nickehallgren/halpis-intcm/hw/bp/images/2024_7_battery_connector_v1_1_3d.png

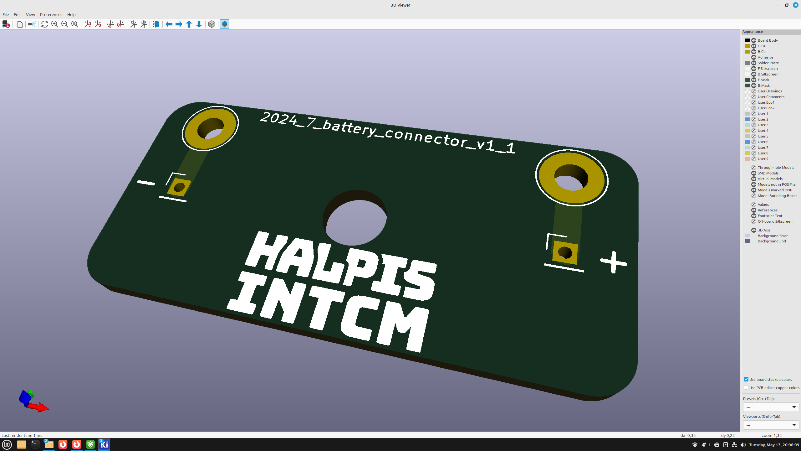
hw/bp/images/2024_7_battery_connector_v1_1_3d.png
