nickehallgren/halpis-intcm/hw/bp/images/2024_7_battery_connector_v1_1_front.png

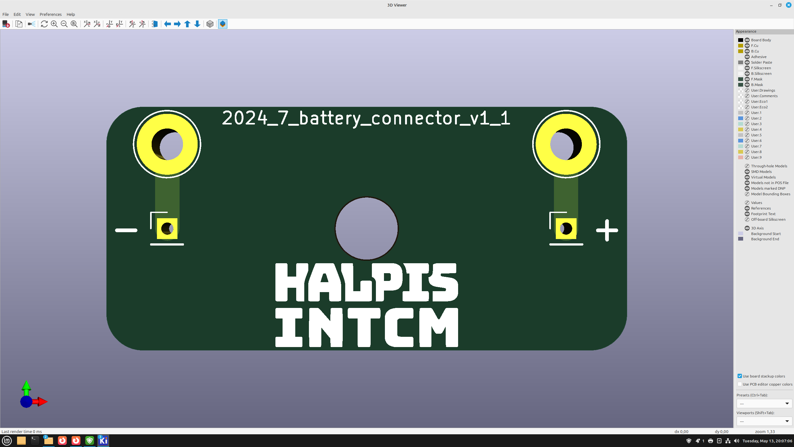
hw/bp/images/2024_7_battery_connector_v1_1_front.png
