nickehallgren/halpis-intcm/hw/bp/images/2024_19_rpi3a_bp_v2_2_3d.png

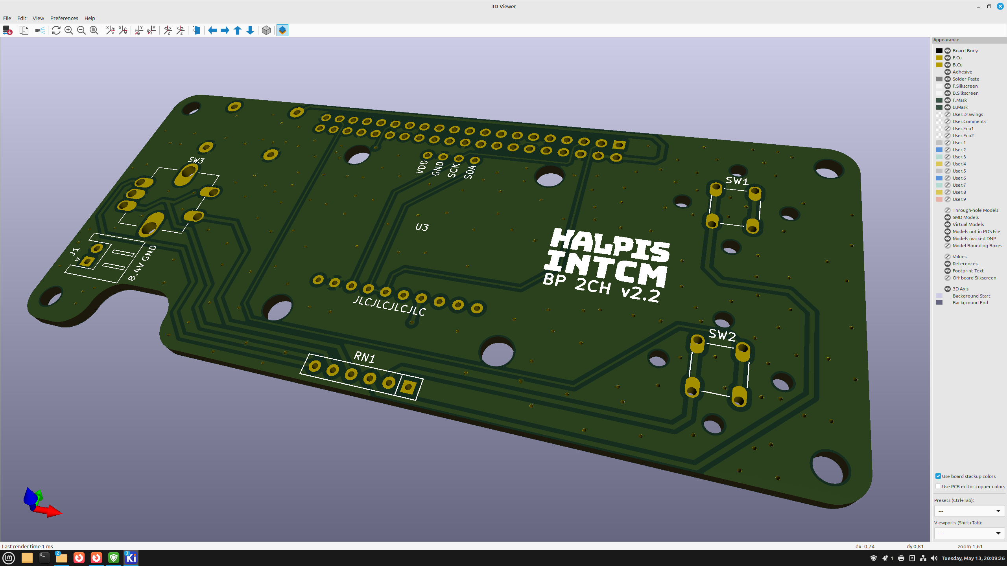
hw/bp/images/2024_19_rpi3a_bp_v2_2_3d.png
