nickehallgren/halpis-intcm/hw/bs/images/2024_15_bs_control_v2.3_3d.png

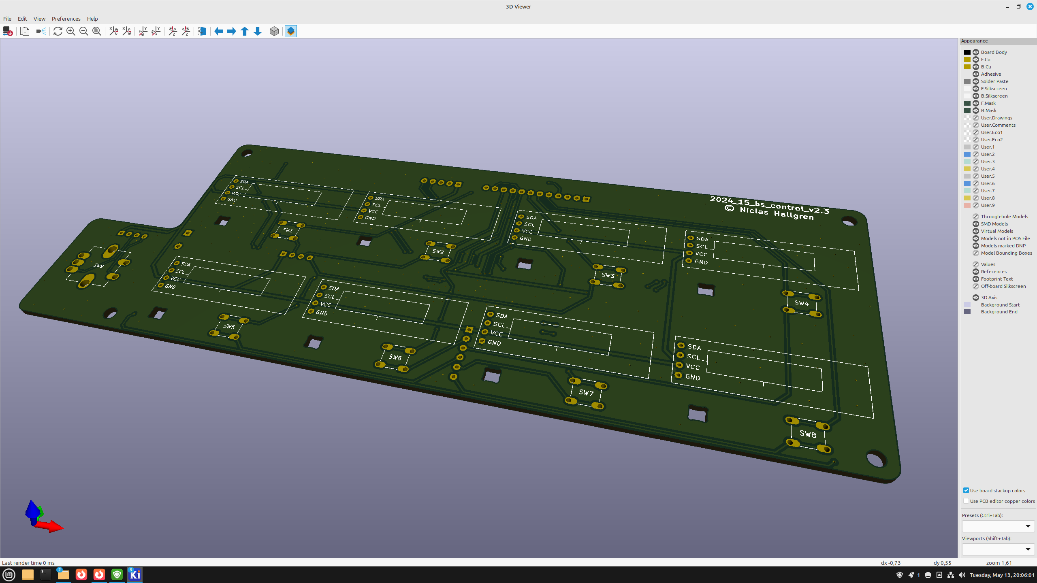
hw/bs/images/2024_15_bs_control_v2.3_3d.png
