nickehallgren/halpis-intcm/hw/bs/images/2024_15_bs_control_v2.3_front.png

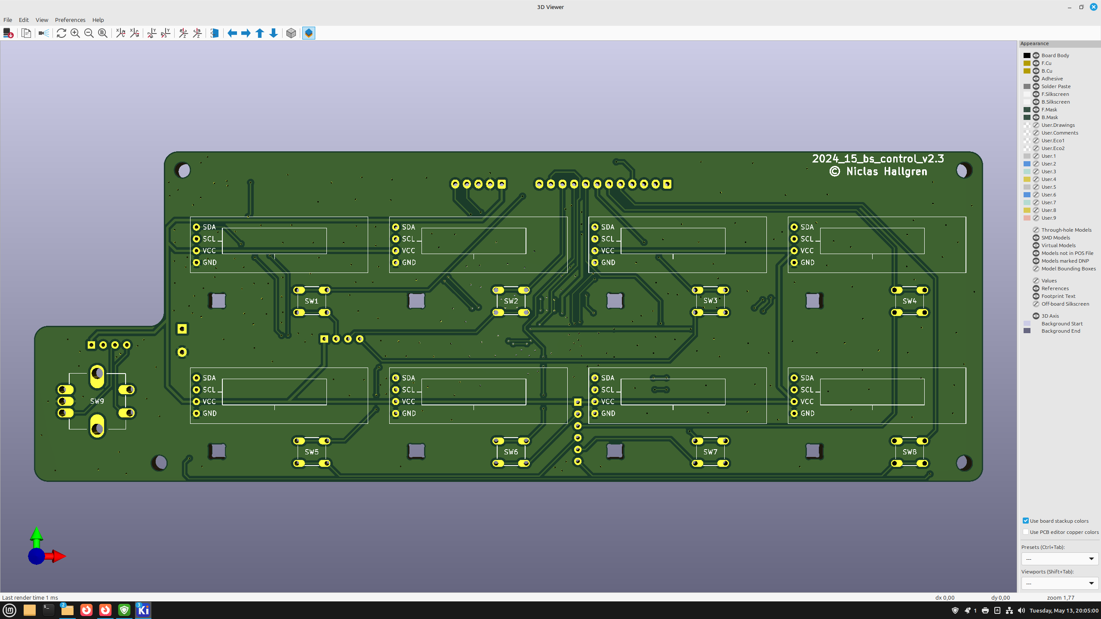
hw/bs/images/2024_15_bs_control_v2.3_front.png
