nickehallgren/halpis-intcm/hw/bs/images/2024_18_rpi3b_bs_v2_4_3d.png

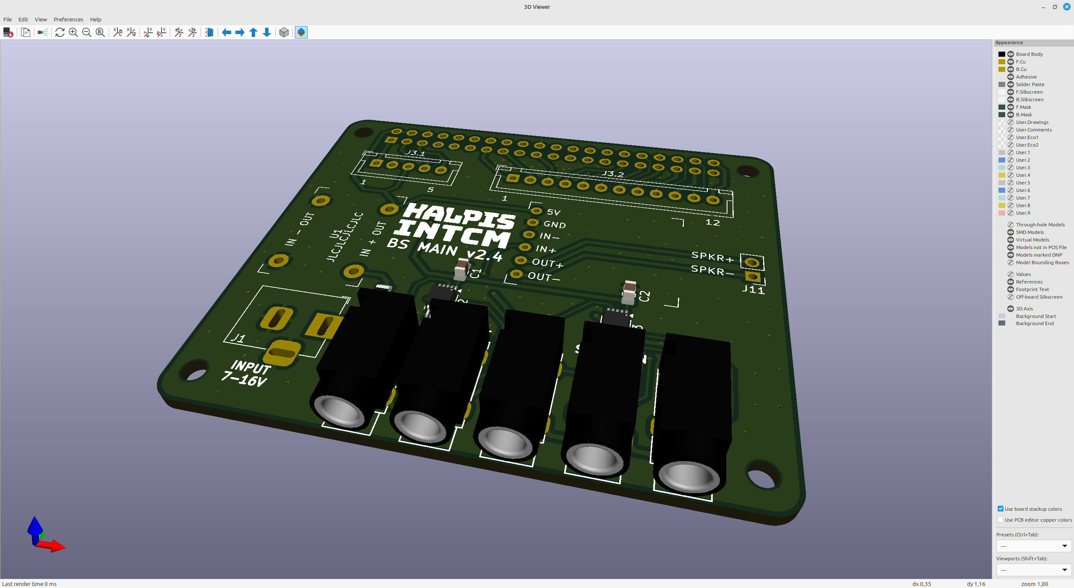
hw/bs/images/2024_18_rpi3b_bs_v2_4_3d.png
