nickehallgren/halpis-intcm/stl/bp/button_foot.stl

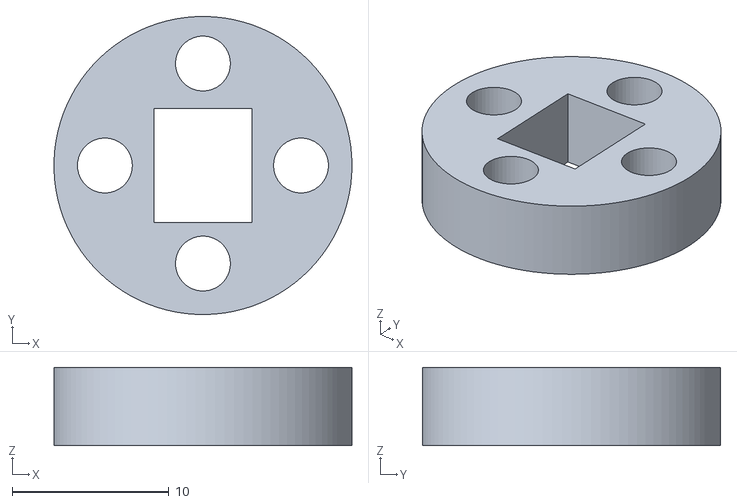
[picture p27: CAD file, 2025-06-03]
stl/bp/button_foot.stl
19.0 x 19.0 x 5.00
