nickehallgren/halpis-intcm/stl/bp/top_v2.stl

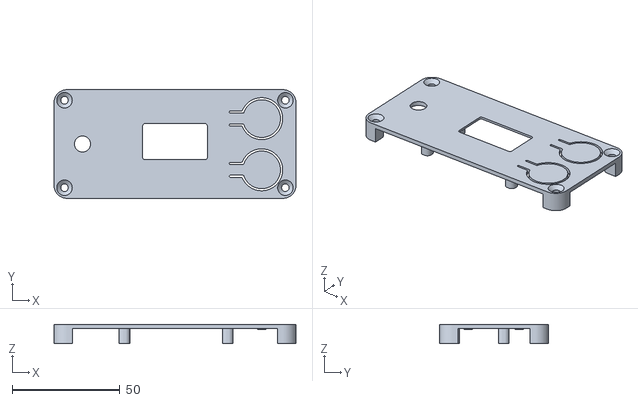
[picture p28: CAD file, 2025-06-03]
stl/bp/top_v2.stl
112.5 x 50.5 x 9.00
