nickehallgren/halpis-intcm/sw/devices/halpis_intcm_setup/ic_menu_bs.py

# This module is part of the HALPIS Intercom project
# Copyright (c) 2024, Niclas Hallgren
# All rights reserved.
#
# This source code is licensed under the MIT license found in the
# LICENSE file in the root directory of this source tree.

menu = {
    0: {
        0: {
            "name": "EXIT MENU",
            "main": 0,
            "sub": 0,
            "active": 0
        },
        1: {
            "name": "BUTTON LOCK",
            "main": 1,
            "sub": 0,
            "active": 0
        },
        2: {
            "name": "MUTE MIC",
            "main": 2,
            "sub": 0,
            "active": 0
        },
        3: {
            "name": "HEADSET",
            "main": 3,
            "sub": 0,
            "active": 0
        },
        4: {
            "name": "MIC LEVEL",
            "main": 4,
            "sub": 0,
            "active": 0
        },
        5: {
            "name": "SHUT DOWN",
            "main": 5,
            "sub": 0,
            "active": 0
        },
        6: {
            "name": "IP",
            "main": 6,
            "sub": 0,
            "active": 0
        },
        7: {
            "name": "DEVICE",
            "main": 7,
            "sub": 0,
            "active": 0
        }
    },
    1: {
        0: {
            "name": "MAIN MENU",
            "main": 0,
            "sub": 1,
            "active": 1
        },
        1: {
            "name": "LOCK 1 OFF",
            "main": 1,
            "sub": 1,
            "active": 1
        },
        2: {
            "name": "LOCK 2 OFF",
            "main": 1,
            "sub": 2,
            "active": 2
        },
        3: {
            "name": "LOCK 3 OFF",
            "main": 1,
            "sub": 3,
            "active": 3
        },
        4: {
            "name": "LOCK 4 OFF",
            "main": 1,
            "sub": 4,
            "active": 4
        },
        5: {
            "name": "LOCK 5 OFF",
            "main": 1,
            "sub": 5,
            "active": 5
        },
        6: {
            "name": "LOCK 6 OFF",
            "main": 1,
            "sub": 6,
            "active": 6
        },
        7: {
            "name": "LOCK 7 OFF",
            "main": 1,
            "sub": 7,
            "active": 7
        },
        8: {
            "name": "LOCK 8 OFF",
            "main": 1,
            "sub": 8,
            "active": 8
        }
    },
    2: {},
    3: {
        0: {
            "name": "MAIN MENU",
            "main": 0,
            "sub": 3,
            "active": 3
        },
        1: {
            "name": "HEADSET ON",
            "main": 3,
            "sub": 1,
            "active": 1
        }
    },
    4: {
        0: {
            "name": "MAIN MENU",
            "main": 0,
            "sub": 4,
            "active": 4
        },
        1: {
            "name": "SET MIC LEVEL",
            "main": 4,
            "sub": 1,
            "active": 1
        }
    },
    5: {
        0: {
            "name": "MAIN MENU",
            "main": 0,
            "sub": 5,
            "active": 5
        },
        1: {
            "name": "SHUT DOWN",
            "main": 5,
            "sub": 1,
            "active": 1
        }
    }
}
